SkyeCA/HapticPuck/PCB/Mini D1 Puck.kicad_sch

## KiCad design PCB/Mini D1 Puck.kicad_sch (2025-06-06)

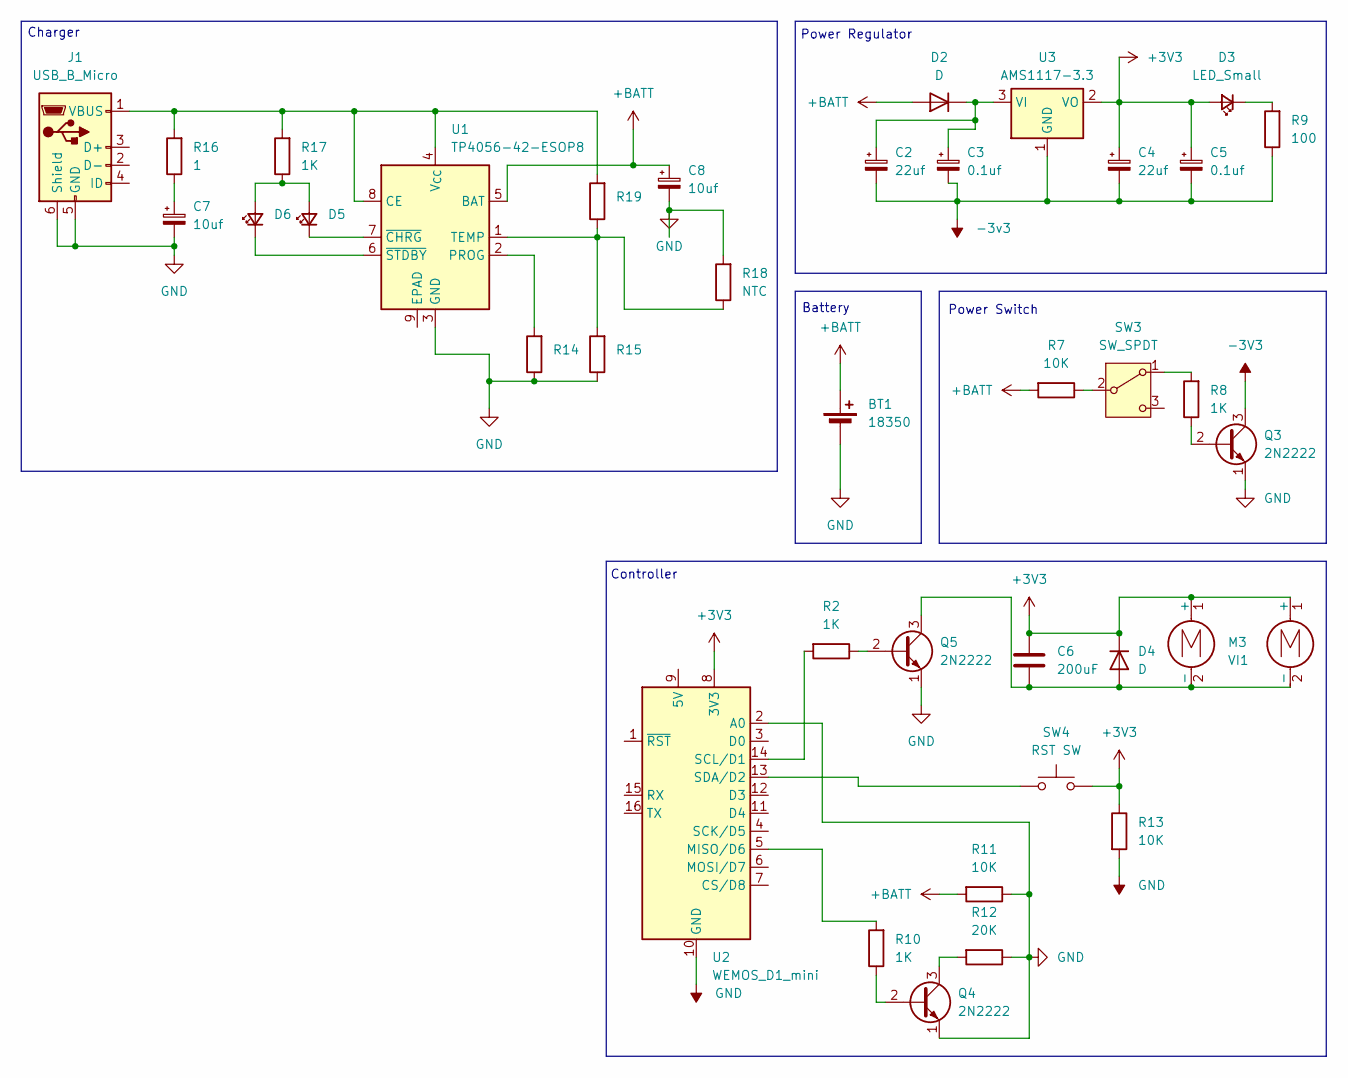
[picture p7: schematic Mini D1 Puck.kicad_sch]

Parts:
BT1: 18350
C2, C4: 22uf
C3, C5: 0.1uf
C6: 200uF
C7, C8: 10uf
D2, D4: D
D3: LED_Small
D5, D6: (no value)
J1: USB_B_Micro
M3: VI1
M4: VI2
Q3, Q4, Q5: 2N2222
R2, R8, R10, R17: 1K
R7, R11, R13: 10K
R9: 100
R12: 20K
R14, R15, R19: (no value)
R16: 1
R18: NTC
SW3: SW_SPDT
SW4: RST SW
U1: TP4056-42-ESOP8; SOIC-8-1EP_3.9x4.9mm_P1.27mm_EP2.41x3.3mm_ThermalVias
U2: WEMOS_D1_mini; WEMOS_D1_mini_light
U3: AMS1117-3.3; SOT-223-3_TabPin2

Connections:
+3V3: C4.1, C5.1, C6.1, D3.2 (A), D4.1 (K), M3.1 (+), M4.1 (+), R13.1, SW4.2, U2.8 (3V3), U3.2 (VO)
+BATT: BT1.1 (+), C8.1, D2.2 (A), R7.2, R11.2, U1.5 (BAT)
-3v3: C2.2, C3.2, C4.2, C5.2, Q3.3 (C), R9.1, U3.1 (GND)
GND: BT1.2 (-), C7.2, C8.2, J1.5 (GND), J1.6 (Shield), Q3.1 (E), Q4.1 (E), Q5.1 (E), R11.1, R12.1, R13.2, R14.1, R15.1, R18.2, U1.3 (GND), U2.2 (A0), U2.10 (GND)
unnamed: C2.1, C3.1, D2.1 (K), U3.3 (VI)
unnamed: C6.2, D4.2 (A), M3.2 (-), M4.2 (-), Q5.3 (C)
unnamed: C7.1, R16.1
unnamed: D3.1 (K), R9.2
unnamed: D5.1 (K), U1.7 (~CHRG)
unnamed: D5.2 (A), D6.2 (A), R17.1
unnamed: D6.1 (K), U1.6 (~STDBY)
unnamed: J1.1 (VBUS), R16.2, R17.2, R19.2, U1.4 (V_{CC}), U1.8 (CE)
unnamed: Q3.2 (B), R8.1
unnamed: Q4.2 (B), R10.1
unnamed: Q4.3 (C), R12.2
unnamed: Q5.2 (B), R2.1
unnamed: R2.2, U2.14 (SCL/D1)
unnamed: R7.1, SW3.2 (B)
unnamed: R8.2, SW3.1 (A)
unnamed: R10.2, U2.5 (MISO/D6)
unnamed: R14.2, U1.2 (PROG)
unnamed: R15.2, R18.1, R19.1, U1.1 (TEMP)
unnamed: SW4.1, U2.13 (SDA/D2)

Notes on the sheet:
Controller
Power Regulator
Charger
Power Switch
Battery
